Ace4896/cloverpad-hardware/notes/notebooks/magnet-distance/magnet-dimensions.png

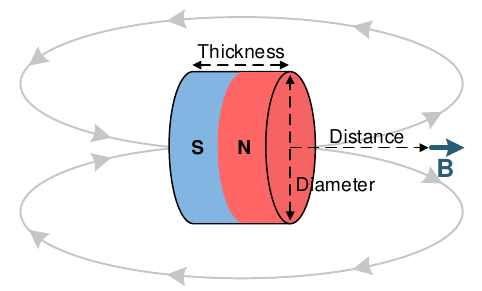
notes/notebooks/magnet-distance/magnet-dimensions.png
