Ace4896/cloverpad-hardware/notes/notebooks/magnet-distance/magnetic-flux-formula.png

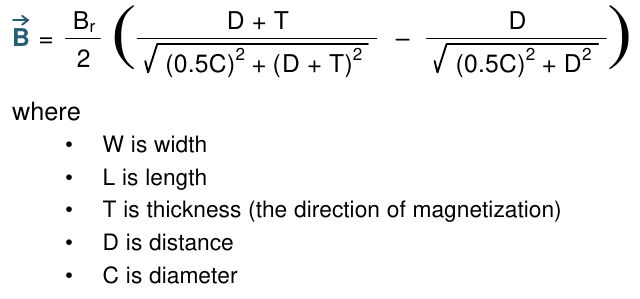
notes/notebooks/magnet-distance/magnetic-flux-formula.png
